davetcc/brooderController/brooderCircuit/ltSpiceSimulations/power-detect-simulation.asc

C1: cap; 2.2µF
C2: cap; 2200µF
D1: diode
Q1: npn; BC547B
R1: res; 20k
R2: res; 10k
R3: res; 15k
R4: res; 20
V1: voltage; SINE(0 12 50 0 0 3 50)
V2: voltage; PULSE(5 0 1 3 0 3 0 1)
Named nets: 0, PWR_OFF
.tran 3
