davetcc/brooderController/brooderCircuit/brooder-mainboard/brooder-mainboard.kicad_pcb

## KiCad design Schematic/XL4016X2Single.sch

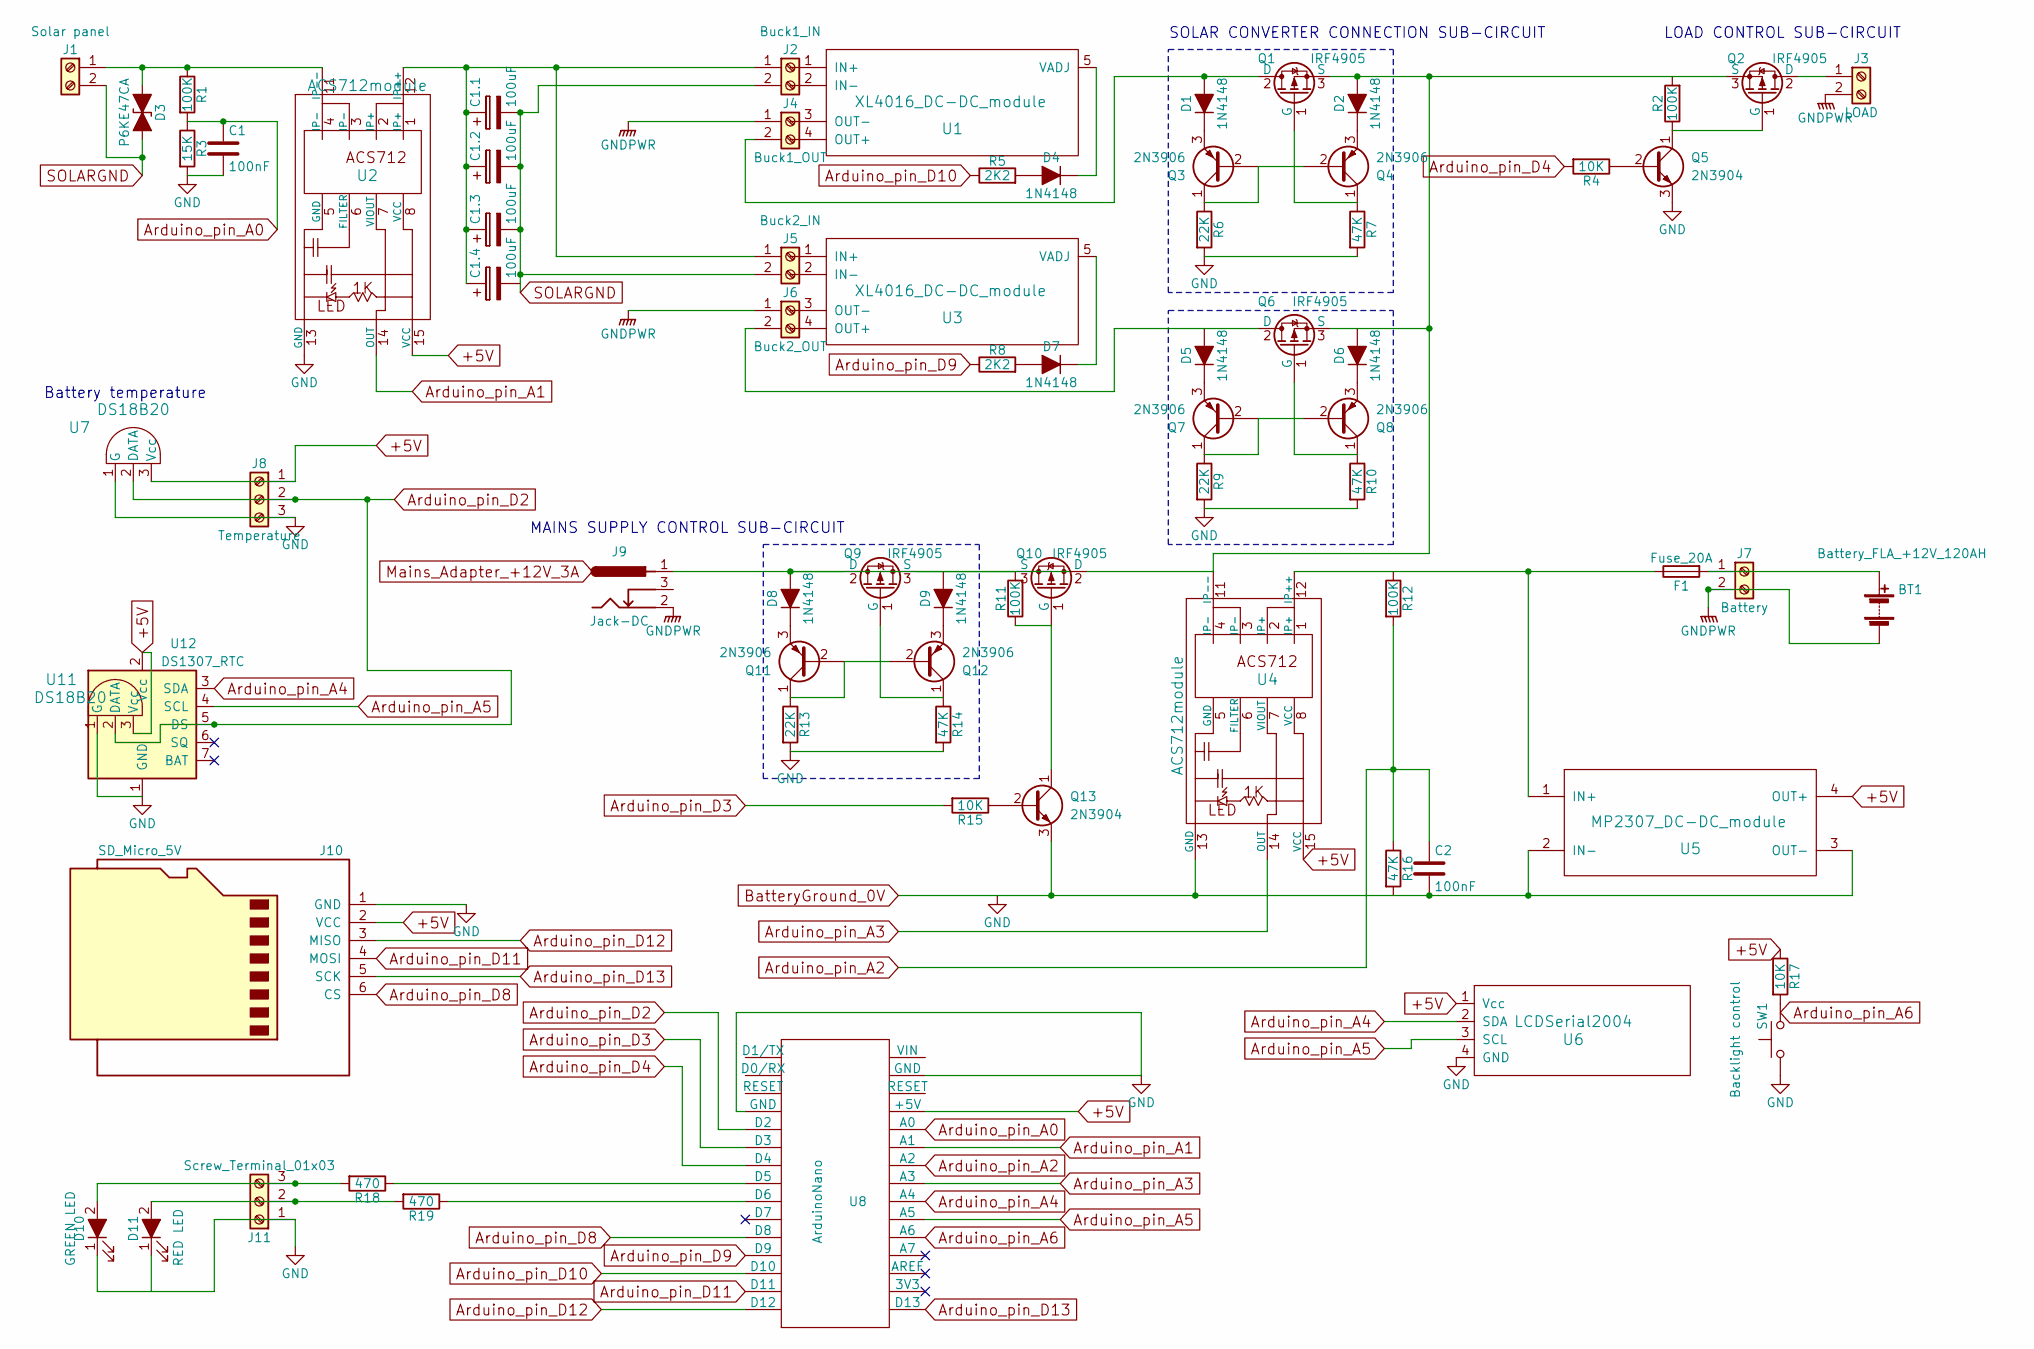
[picture p12: schematic XL4016X2Single.sch]

Parts:
BT1: Battery_FLA_+12V_120AH
C1, C2: 100nF
C1.1, C1.2, C1.3, C1.4: 100uF
D1, D2, D4, D5, D6, D7, D8, D9: 1N4148
D3: P6KE47CA
D10: GREEN LED
D11: RED LED
F1: Fuse_20A
J1: Solar panel
J2: Buck1_IN
J3: LOAD
J4: Buck1_OUT
J5: Buck2_IN
J6: Buck2_OUT
J7: Battery
J8: Temperature
J9: Jack-DC
J10: SD_Micro_5V
J11: Screw_Terminal_01x03
Q1, Q2, Q6, Q9, Q10: IRF4905; TO-220_Vertical
Q3, Q4, Q7, Q8, Q11, Q12: 2N3906
Q5, Q13: 2N3904
R1, R2, R11, R12: 100K
R3: 15K
R4, R15, R17: 10K
R5, R8: 2K2
R6, R9, R13: 22K
R7, R10, R14, R16: 47K
R18, R19: 470
SW1: Backlight control
U1, U3: XL4016_DC-DC_module
U2, U4: ACS712module
U5: MP2307_DC-DC_module
U6: LCDSerial2004
U7, U11: DS18B20
U8: ArduinoNano
U12: DS1307_RTC

Connections:
+5V: J8.1, J10.2 (VCC), R17.1, U2.15 (VCC), U4.15 (VCC), U5.4 (OUT+), U6.1 (Vcc), U7.3 (Vcc), U8.27 (+5V), U11.3 (Vcc), U12.2 (Vcc)
Arduino_pin_A0: C1.1, R1.2, R3.1, U8.26 (A0)
Arduino_pin_A1: U2.14 (OUT), U8.25 (A1)
Arduino_pin_A2: C2.1, R12.2, R16.1, U8.24 (A2)
Arduino_pin_A3: U4.14 (OUT), U8.23 (A3)
Arduino_pin_A4: U6.2 (SDA), U8.22 (A4), U12.3 (SDA)
Arduino_pin_A5: U6.3 (SCL), U8.21 (A5), U12.4 (SCL)
Arduino_pin_A6: U8.20 (A6)
Arduino_pin_D2: J8.2, U7.2 (DATA), U8.5 (D2), U11.2 (DATA), U12.5 (DS)
Arduino_pin_D3: R15.2, U8.5 (D2)
Arduino_pin_D4: R4.2, U8.7 (D4)
Arduino_pin_D8: J10.6 (CS), U8.11 (D8)
Arduino_pin_D9: R8.1, U8.12 (D9)
Arduino_pin_D10: R5.1, U8.13 (D10)
Arduino_pin_D11: J10.4 (MOSI), U8.14 (D11)
Arduino_pin_D12: J10.3 (MISO), U8.15 (D12)
Arduino_pin_D13: J10.5 (SCK), U8.16 (D13)
BatteryGround_0V: C1.2, C2.2, D10.1 (K), J8.3, J10.1 (GND), J11.1, Q5.3 (E), Q13.3 (E), R3.2, R6.2, R7.2, R9.2, R10.2, R13.2, R14.2, SW1.1, U2.13 (GND), U4.13 (GND), U5.2 (IN-), U5.3 (OUT-), U6.4 (GND), U7.1 (G), U8.4 (GND), U8.29 (GND), U11.1 (G), U12.1 (GND)
GNDPWR: BT1.2 (-), J3.2, J4.1, J6.1, J7.2, J9.2
unnamed: BT1.1 (+), F1.2, J7.1
unnamed: C1.1.1, C1.2.1, C1.3.1, C1.4.1, J2.1, J5.1, U2.12 (IP++)
unnamed: D1.1 (K), Q3.3 (E)
unnamed: D1.2 (A), J4.2, Q1.2 (D)
unnamed: D2.1 (K), Q4.3 (E)
unnamed: D2.2 (A), Q1.3 (S), Q2.3 (S), Q6.3 (S), Q10.2 (D), U4.11 (IP--)
unnamed: D3.1 (A1), J1.1, R1.1, U2.11 (IP--)
unnamed: D4.1 (K), U1.5 (VADJ)
unnamed: D4.2 (A), R5.2
unnamed: D5.1 (K), Q7.3 (E)
unnamed: D6.1 (K), Q8.3 (E)
unnamed: D7.1 (K), U3.5 (VADJ)
unnamed: D7.2 (A), R8.2
unnamed: D8.1 (K), Q11.3 (E)
unnamed: D8.2 (A), J9.1, Q9.2 (D)
unnamed: D9.1 (K), Q12.3 (E)
unnamed: D10.2 (A), J11.3, R18.2
unnamed: D11.2 (A), J11.2, R19.2
unnamed: F1.1, U4.12 (IP++), U5.1 (IN+)
unnamed: J3.1, Q2.2 (D)
unnamed: J6.2, Q6.2 (D)
unnamed: Q1.1 (G), Q4.1 (C), R7.1
unnamed: Q2.1 (G), Q5.1 (C), R2.1
unnamed: Q3.1 (C), Q3.2 (B), Q4.2 (B), R6.1
unnamed: Q5.2 (B), R4.1
unnamed: Q6.1 (G), Q8.1 (C), R10.1
unnamed: Q7.1 (C), Q7.2 (B), Q8.2 (B), R9.1
unnamed: Q10.1 (G), Q13.1 (C), R11.1
unnamed: Q9.3 (S), Q10.3 (S), R11.2
unnamed: Q11.1 (C), Q11.2 (B), Q12.2 (B), R13.1
unnamed: Q9.1 (G), Q12.1 (C), R14.1
unnamed: Q13.2 (B), R15.1
unnamed: R17.2, SW1.2
unnamed: R18.1, U8.8 (D5)
unnamed: R19.1, U8.9 (D6)
SOLARGND: C1.1.2, C1.2.2, C1.3.2, D3.2 (A2), J1.2, J2.2, J5.2

Notes on the sheet:
Battery temperature
LOAD CONTROL SUB-CIRCUIT
MAINS SUPPLY CONTROL SUB-CIRCUIT
SOLAR CONVERTER CONNECTION SUB-CIRCUIT
