davetcc/brooderController/designs/doorAssembly1.jpg

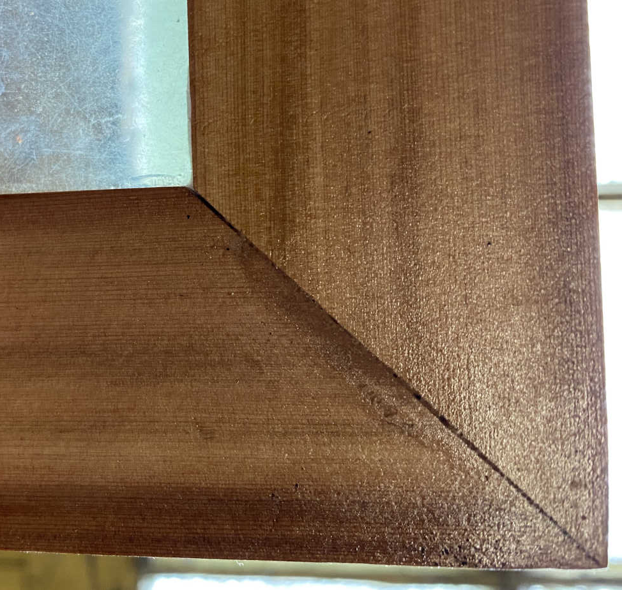
designs/doorAssembly1.jpg
